gurues/Termostato-Broker-Blynk_IOT/Ayuda/Fotos/01-Shelly_1_Tasmota.jpg

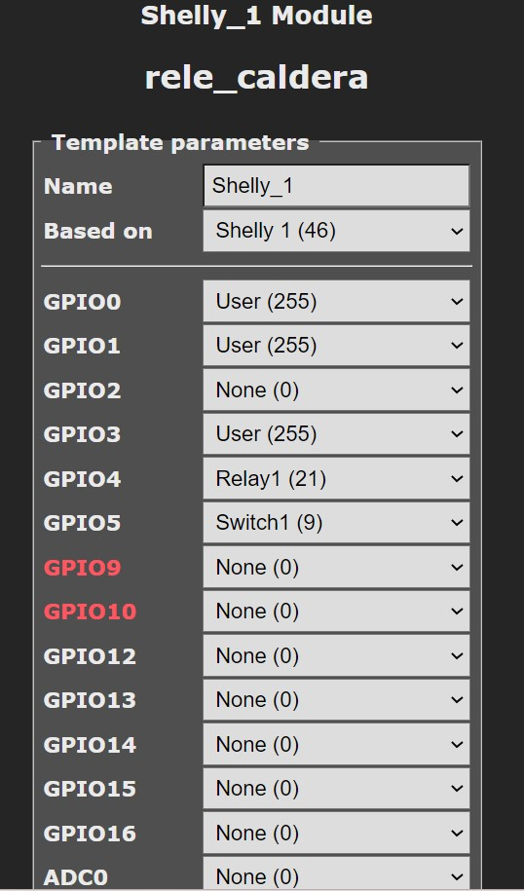
Ayuda/Fotos/01-Shelly_1_Tasmota.jpg
