gurues/Termostato-Broker-Blynk_IOT/Ayuda/Fotos/02-Shelly_1_Tasmota.jpg

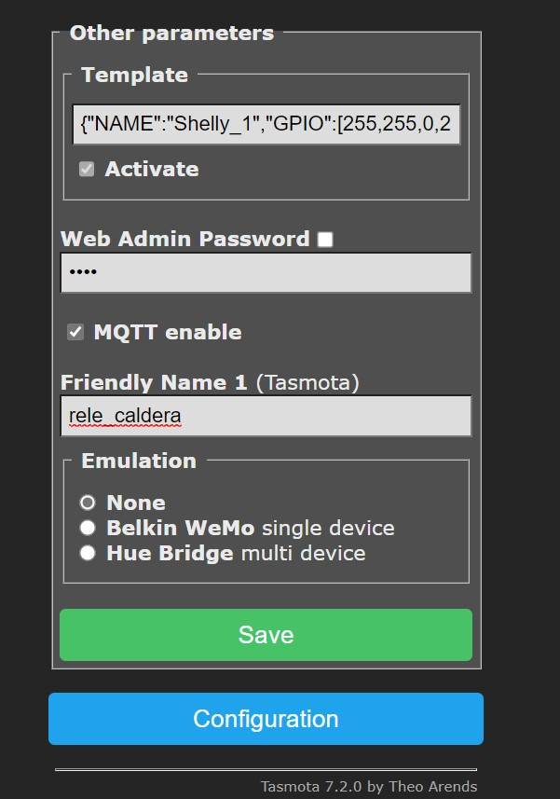
Ayuda/Fotos/02-Shelly_1_Tasmota.jpg
