gurues/Termostato-Broker-Blynk_IOT/Ayuda/Fotos/04-Shelly_1_Tasmota.jpg

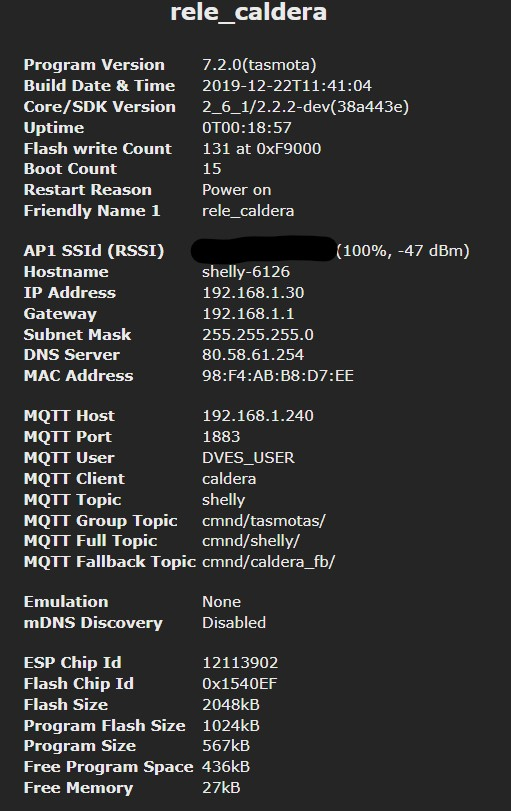
Ayuda/Fotos/04-Shelly_1_Tasmota.jpg
