gurues/Termostato-Broker-Blynk_IOT/Ayuda/Fotos/05-Shelly_1_Tasmota.jpg

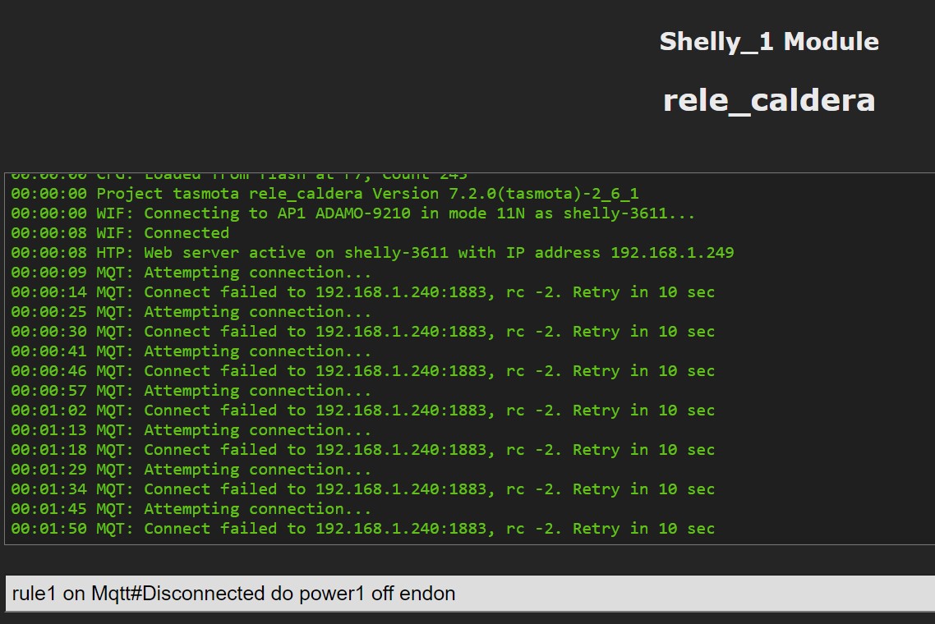
Ayuda/Fotos/05-Shelly_1_Tasmota.jpg
