gurues/Termostato-Broker-Blynk_IOT/Ayuda/Fotos/06-Shelly_1_Tasmota.jpg

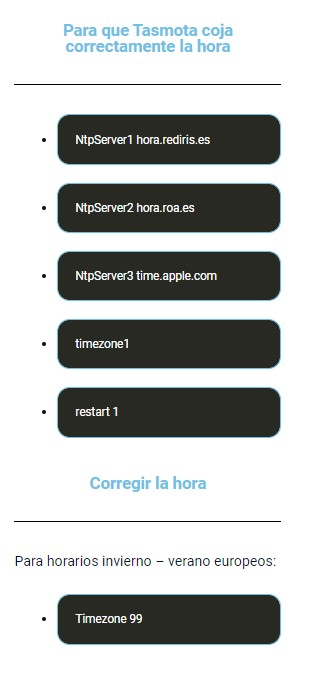
Ayuda/Fotos/06-Shelly_1_Tasmota.jpg
