gurues/Termostato-Broker-Blynk_IOT/Ayuda/Fotos/07-Termostato-Broker.jpg

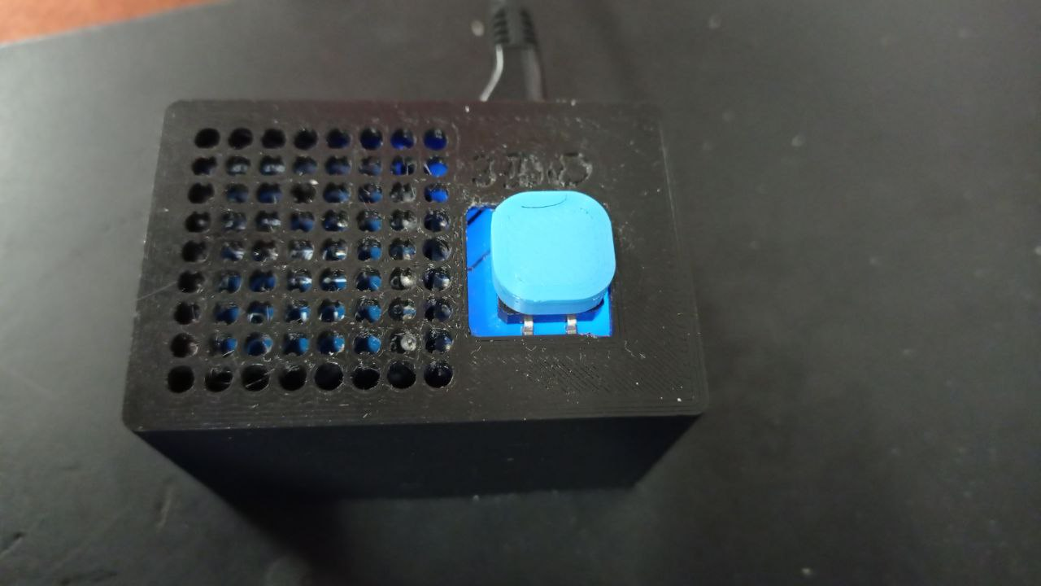
Ayuda/Fotos/07-Termostato-Broker.jpg
