gurues/Termostato-Broker-Blynk_IOT/Ayuda/Fotos/08-Termostato-Broker.jpg

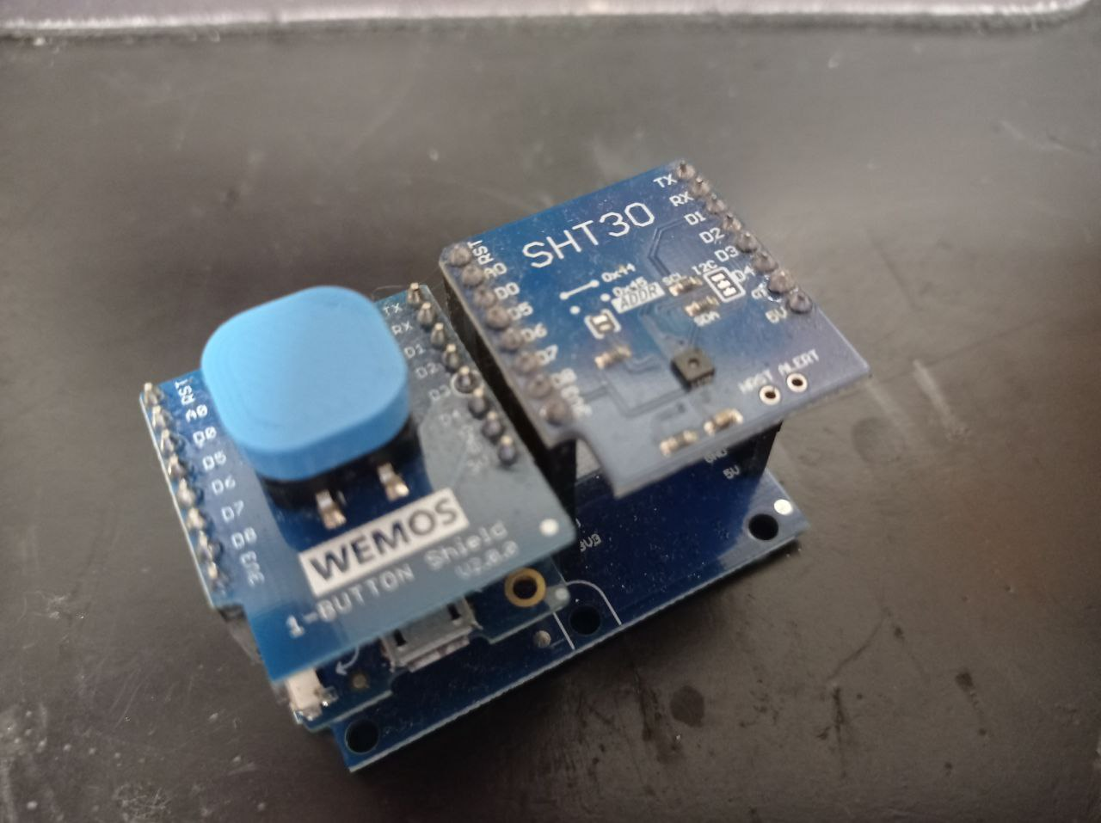
Ayuda/Fotos/08-Termostato-Broker.jpg
