gurues/Termostato-Broker-Blynk_IOT/Ayuda/Fotos/09-Termostato-Broker.jpg

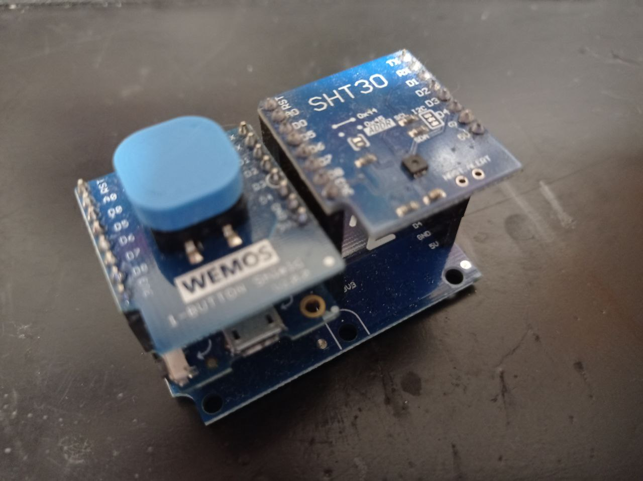
Ayuda/Fotos/09-Termostato-Broker.jpg
