gurues/Termostato-Broker-Blynk_IOT/Ayuda/Fotos/11-Termostato-Broker.jpg

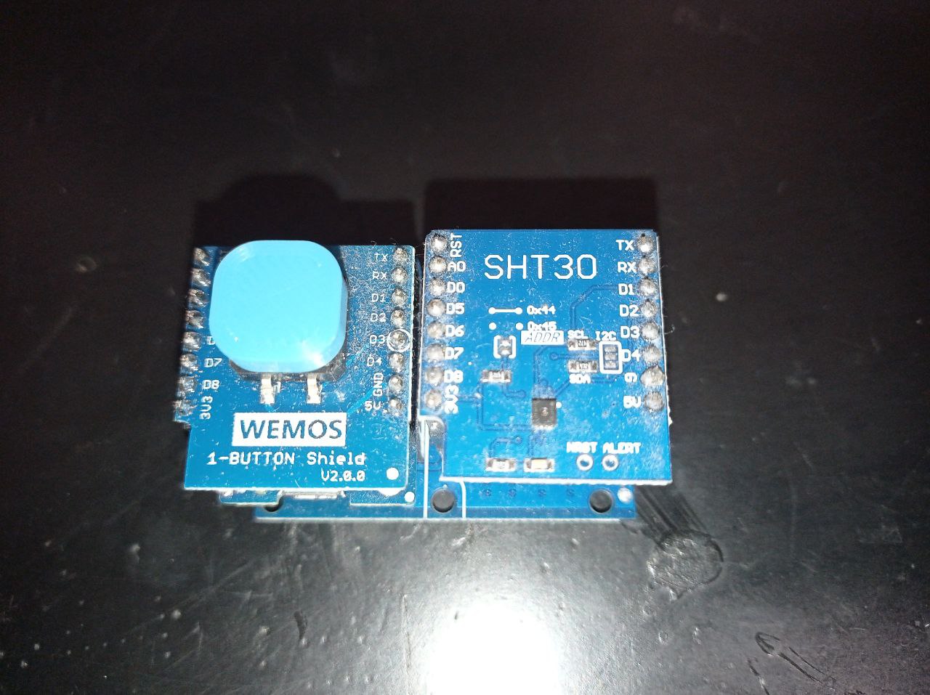
Ayuda/Fotos/11-Termostato-Broker.jpg
