gurues/Termostato-Broker-Blynk_IOT/Ayuda/Fotos/12-App-Blynk.jpg

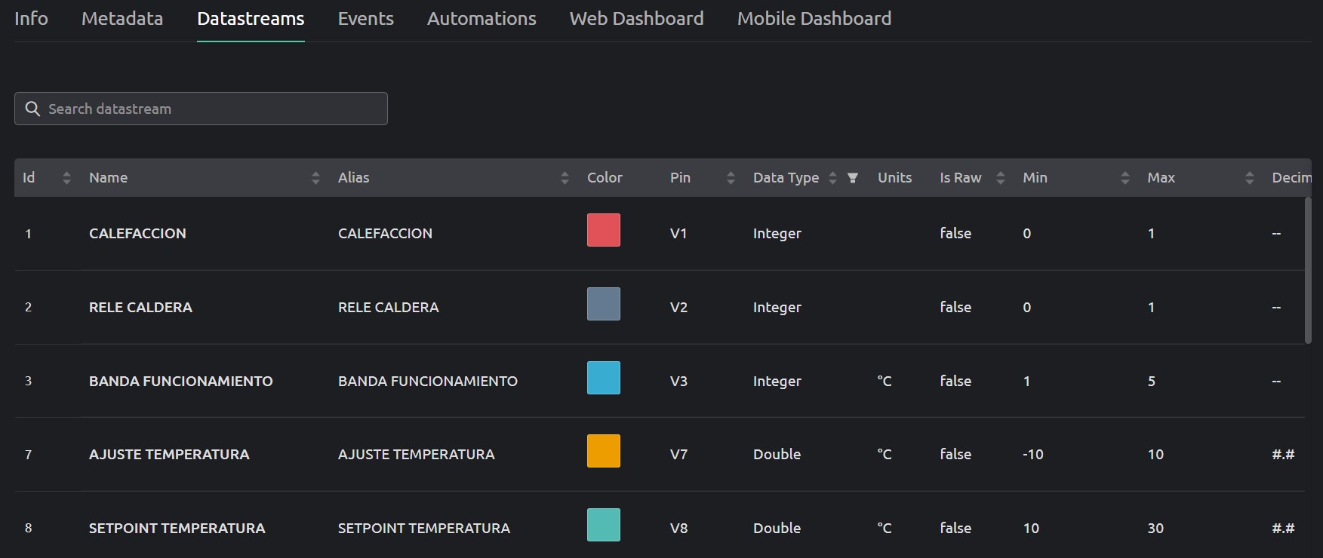
Ayuda/Fotos/12-App-Blynk.jpg
