gurues/Termostato-Broker-Blynk_IOT/Ayuda/Fotos/13-App-Blynk.jpg

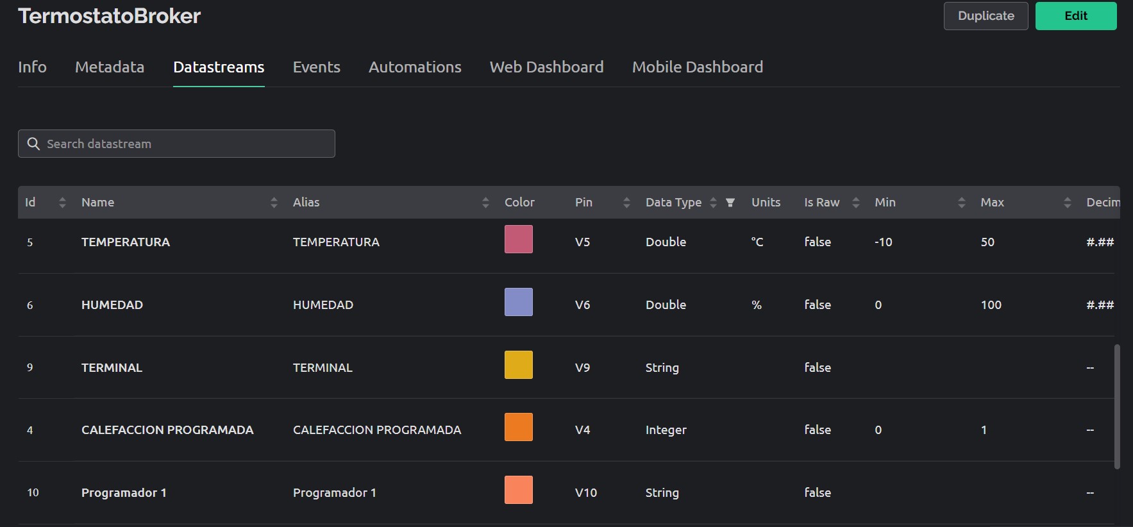
Ayuda/Fotos/13-App-Blynk.jpg
