gurues/Termostato-Broker-Blynk_IOT/Ayuda/Fotos/14-App-Blynk.jpg

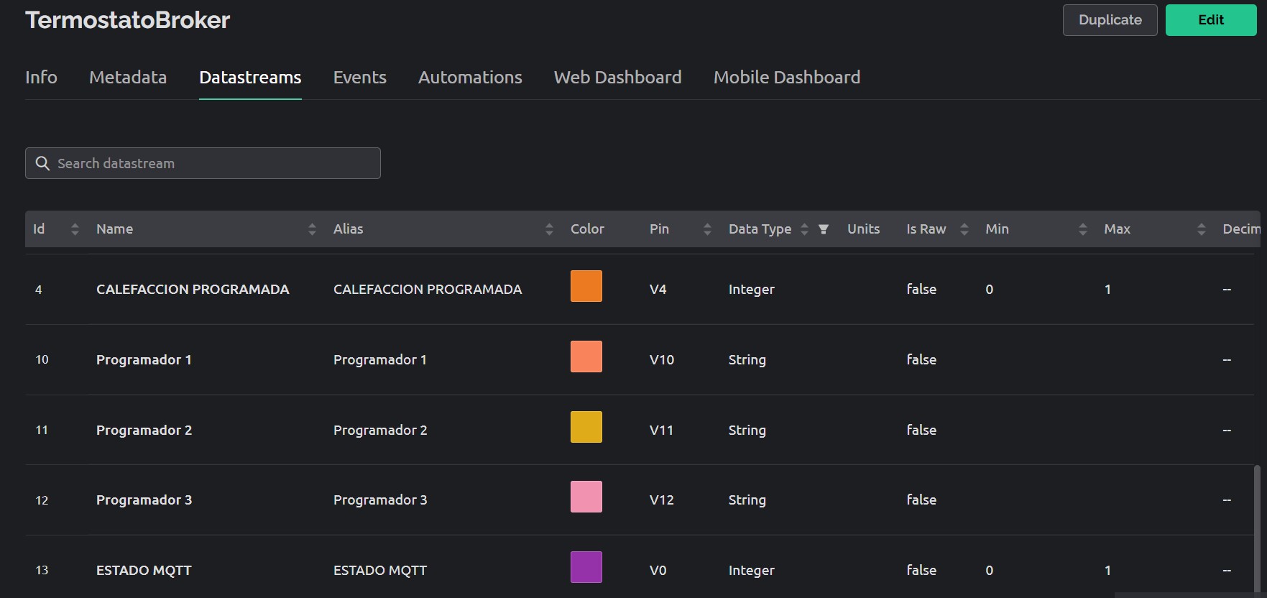
Ayuda/Fotos/14-App-Blynk.jpg
