gurues/Termostato-Broker-Blynk_IOT/Ayuda/Fotos/16-App-Blynk.jpg

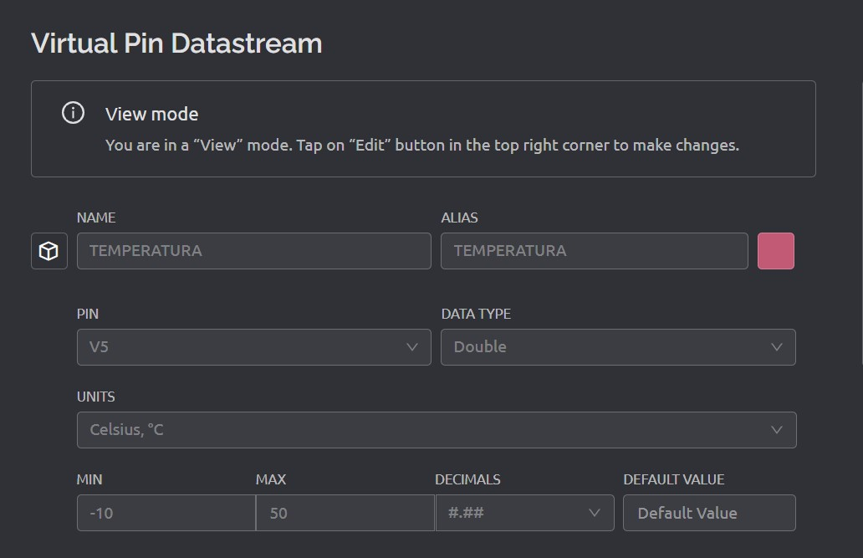
Ayuda/Fotos/16-App-Blynk.jpg
