gurues/Termostato-Broker-Blynk_IOT/Ayuda/Fotos/17-App-Blynk.jpg

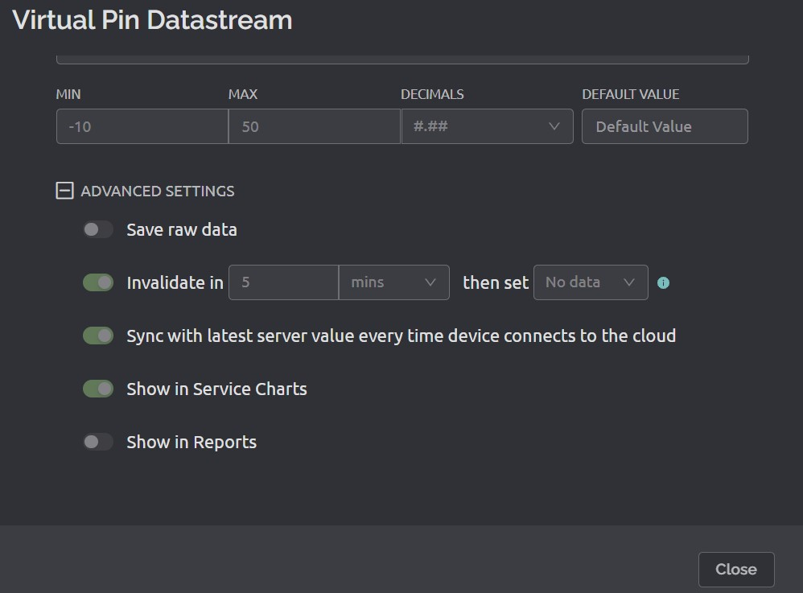
Ayuda/Fotos/17-App-Blynk.jpg
