gurues/Termostato-Broker-Blynk_IOT/Ayuda/Fotos/19-App-Blynk.jpg

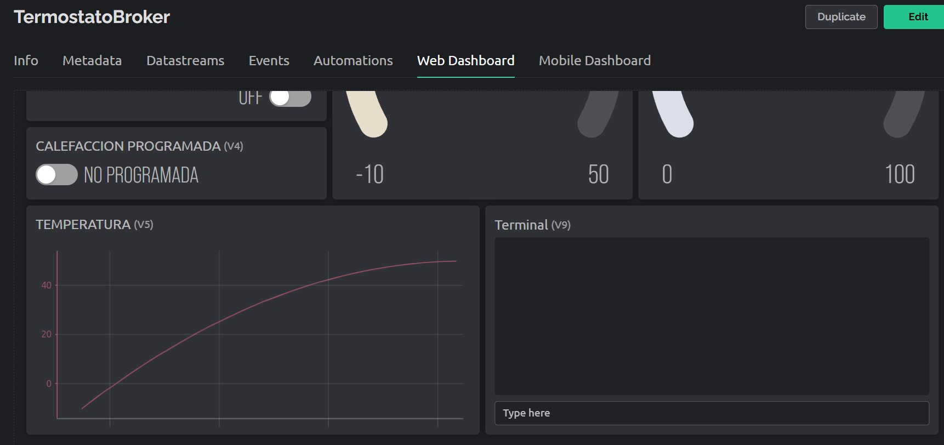
Ayuda/Fotos/19-App-Blynk.jpg
