gurues/Termostato-Broker-Blynk_IOT/Ayuda/Fotos/20-App-Blynk.jpg

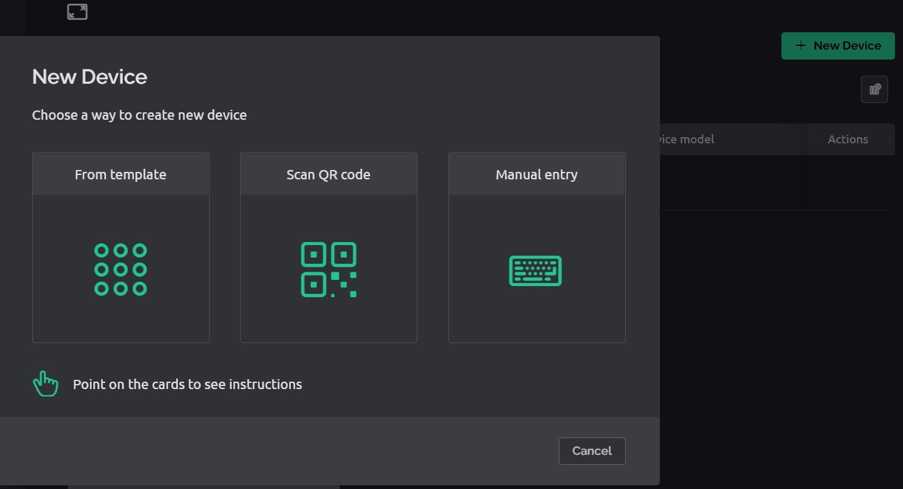
Ayuda/Fotos/20-App-Blynk.jpg
