gurues/Termostato-Broker-Blynk_IOT/Ayuda/Fotos/21-App-Blynk.jpg

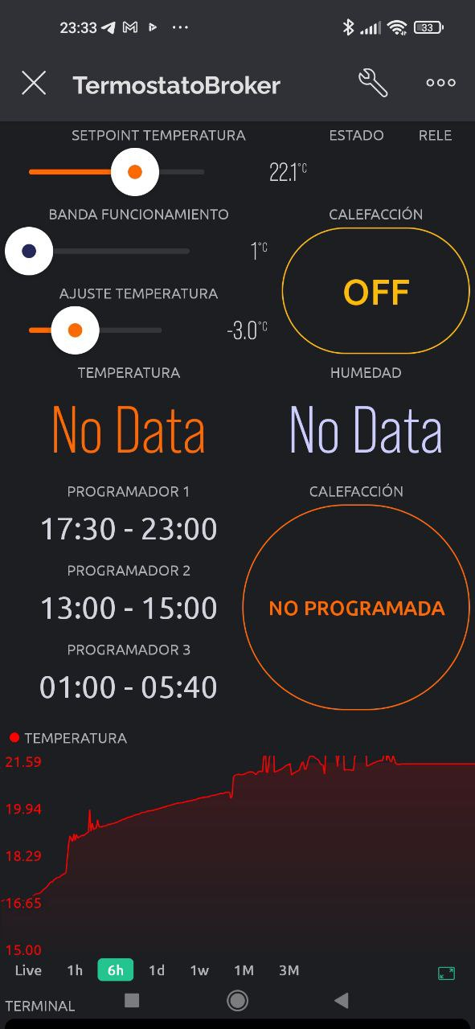
Ayuda/Fotos/21-App-Blynk.jpg
