gurues/Termostato-Broker-Blynk_IOT/Ayuda/Fotos/23-App-Blynk.jpg

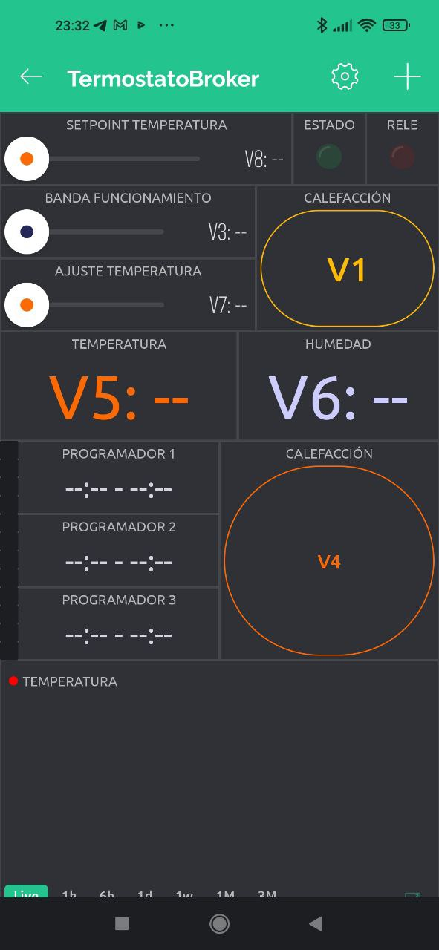
Ayuda/Fotos/23-App-Blynk.jpg
