gurues/Termostato-Broker-Blynk_IOT/Ayuda/Fotos/24-App-Blynk.jpg

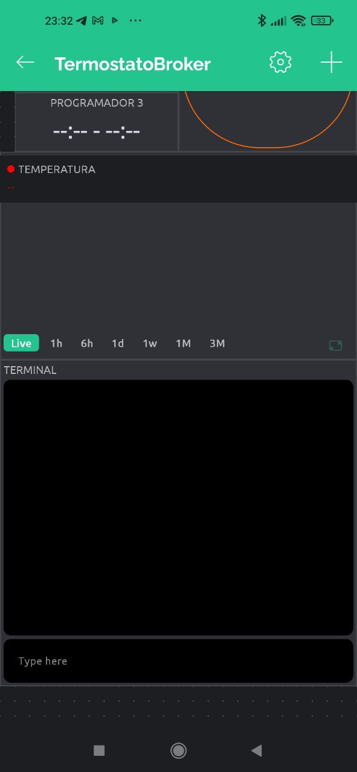
Ayuda/Fotos/24-App-Blynk.jpg
