gurues/Termostato-Broker-Blynk_IOT/Ayuda/Fotos/30-Termostato-Broker.jpg

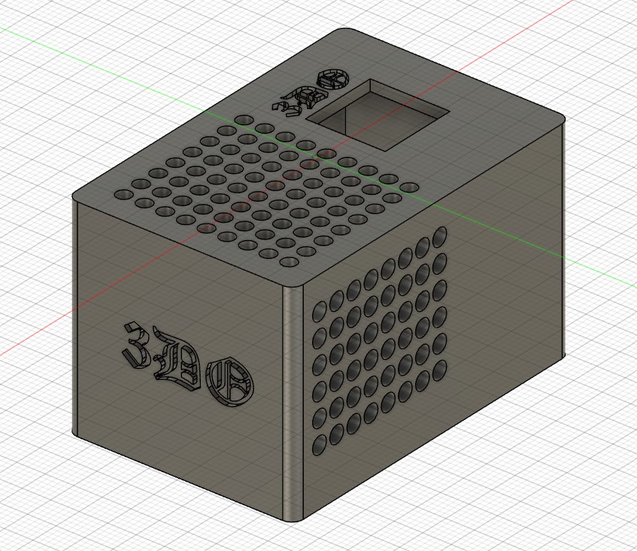
Ayuda/Fotos/30-Termostato-Broker.jpg
