gurues/Termostato-Broker-Blynk_IOT/Ayuda/Fotos/33-App-Blynk_1_0_2.jpg

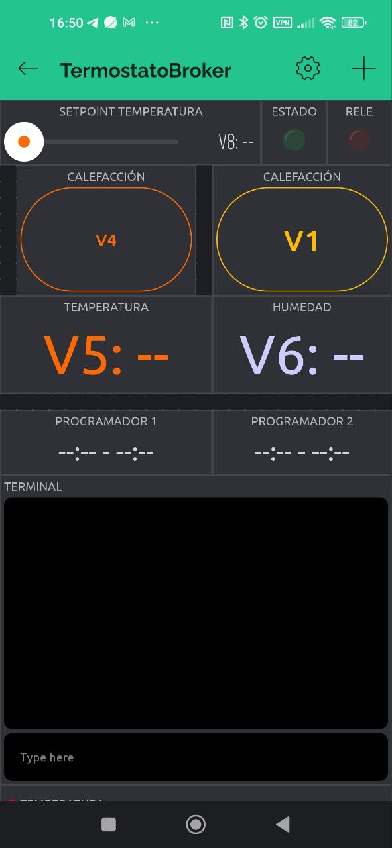
Ayuda/Fotos/33-App-Blynk_1_0_2.jpg
